gbrickell/ESP32_upgrade_to_ESP8266_2WD_robot/ESP32_code/Kranky_Regular_12.h

// changed the character type below from const char to const uint8_t to correct compilation error
const uint8_t Kranky_Regular_12[] PROGMEM = {
	0x0C, // Width: 12
	0x10, // Height: 16
	0x20, // First Char: 32
	0xE0, // Numbers of Chars: 224

	// Jump Table:
	0xFF, 0xFF, 0x00, 0x03,  // 32:65535
	0x00, 0x00, 0x05, 0x03,  // 33:0
	0x00, 0x05, 0x03, 0x02,  // 34:5
	0x00, 0x08, 0x0E, 0x07,  // 35:8
	0x00, 0x16, 0x0A, 0x06,  // 36:22
	0x00, 0x20, 0x0C, 0x06,  // 37:32
	0x00, 0x2C, 0x0E, 0x07,  // 38:44
	0x00, 0x3A, 0x01, 0x01,  // 39:58
	0x00, 0x3B, 0x06, 0x03,  // 40:59
	0x00, 0x41, 0x06, 0x03,  // 41:65
	0x00, 0x47, 0x07, 0x04,  // 42:71
	0x00, 0x4E, 0x0A, 0x05,  // 43:78
	0x00, 0x58, 0x04, 0x02,  // 44:88
	0x00, 0x5C, 0x0A, 0x05,  // 45:92
	0x00, 0x66, 0x04, 0x02,  // 46:102
	0x00, 0x6A, 0x07, 0x04,  // 47:106
	0x00, 0x71, 0x10, 0x08,  // 48:113
	0x00, 0x81, 0x08, 0x05,  // 49:129
	0x00, 0x89, 0x0C, 0x07,  // 50:137
	0x00, 0x95, 0x0C, 0x07,  // 51:149
	0x00, 0xA1, 0x0E, 0x07,  // 52:161
	0x00, 0xAF, 0x0C, 0x06,  // 53:175
	0x00, 0xBB, 0x0C, 0x07,  // 54:187
	0x00, 0xC7, 0x0D, 0x07,  // 55:199
	0x00, 0xD4, 0x10, 0x08,  // 56:212
	0x00, 0xE4, 0x0C, 0x07,  // 57:228
	0x00, 0xF0, 0x04, 0x02,  // 58:240
	0x00, 0xF4, 0x04, 0x02,  // 59:244
	0x00, 0xF8, 0x06, 0x03,  // 60:248
	0x00, 0xFE, 0x0A, 0x05,  // 61:254
	0x01, 0x08, 0x06, 0x03,  // 62:264
	0x01, 0x0E, 0x09, 0x05,  // 63:270
	0x01, 0x17, 0x12, 0x09,  // 64:279
	0x01, 0x29, 0x10, 0x08,  // 65:297
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
	0x00,0x08,0xF8,0x0F,0xF8,0x0F,0x88,0x08,0xC8,0x01,0x38,	// 70
	0xC0,0x07,0xA0,0x0F,0x50,0x08,0x08,0x10,0x08,0x10,0x08,0x08,0x88,0x08,0x38,0x0F,0x80,	// 71
	0x08,0x0A,0xF8,0x0D,0x08,0x0F,0x80,0x08,0x00,0x01,0x88,0x08,0xF0,0x0F,0x08,0x08,	// 72
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
};
